Youngwer/CASA0021_GPP/APP/assets/images/Animation/R1.png

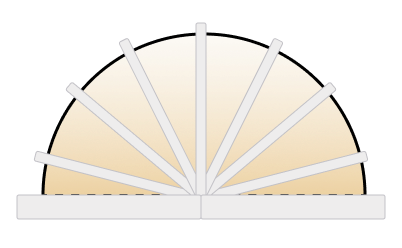
APP/assets/images/Animation/R1.png
