Youngwer/CASA0021_GPP/APP/assets/images/Animation/R3.png

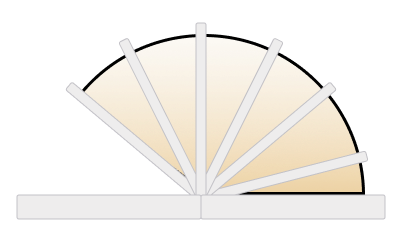
APP/assets/images/Animation/R3.png
