Youngwer/CASA0021_GPP/APP/assets/images/Animation/R6.png

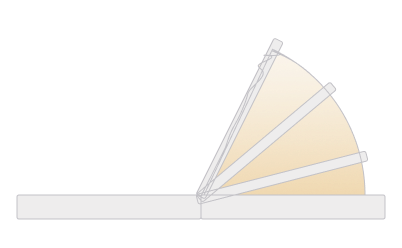
APP/assets/images/Animation/R6.png
