Youngwer/CASA0021_GPP/APP/assets/images/Animation/R7.png

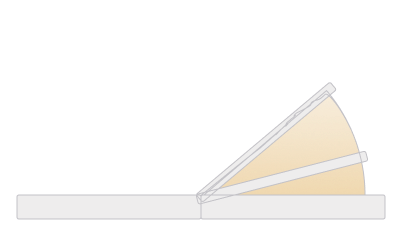
APP/assets/images/Animation/R7.png
