Youngwer/CASA0021_GPP/APP/assets/images/Animation/R8.png

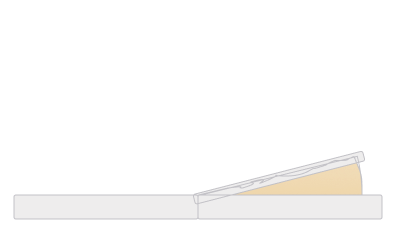
APP/assets/images/Animation/R8.png
