Youngwer/CASA0021_GPP/APP/assets/images/book2_AI.jpg

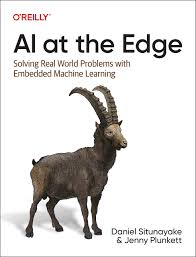
APP/assets/images/book2_AI.jpg
