Youngwer/CASA0021_GPP/APP/assets/images/book3_dominicana.jpg

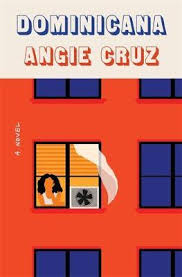
APP/assets/images/book3_dominicana.jpg
