Youngwer/CASA0021_GPP/APP/assets/images/book4_steppenwolf.jpg

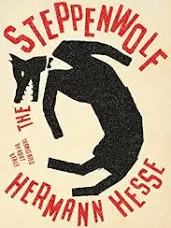
APP/assets/images/book4_steppenwolf.jpg
