Youngwer/CASA0021_GPP/APP/assets/images/book5_west.jpg

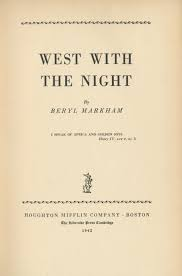
APP/assets/images/book5_west.jpg
