Youngwer/CASA0021_GPP/APP/assets/images/book6_muscle.jpg

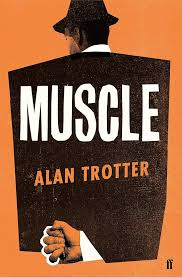
APP/assets/images/book6_muscle.jpg
