Youngwer/CASA0021_GPP/APP/assets/images/Duncan.png

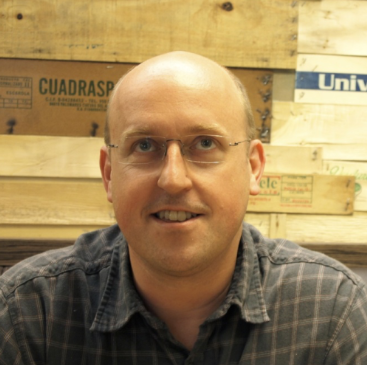
APP/assets/images/Duncan.png
