Youngwer/CASA0021_GPP/APP/assets/images/Home.png

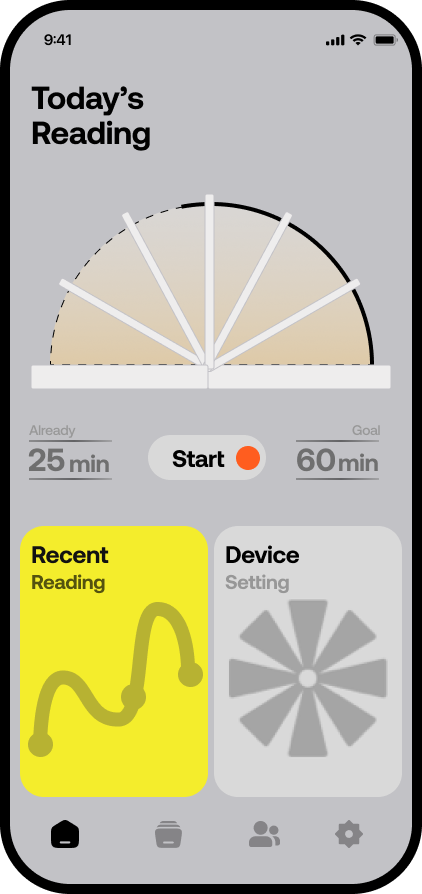
APP/assets/images/Home.png
