Youngwer/CASA0021_GPP/APP/assets/images/image2.jpg

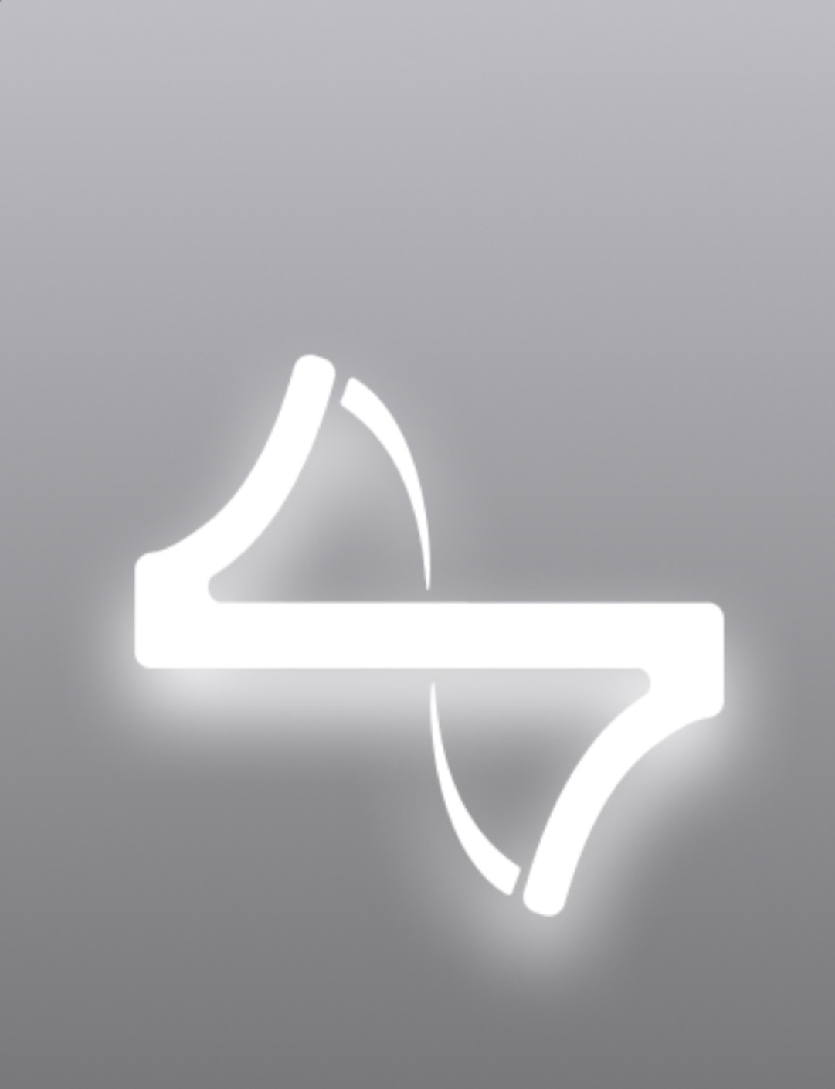
APP/assets/images/image2.jpg
