Youngwer/CASA0021_GPP/APP/assets/images/Ke.png

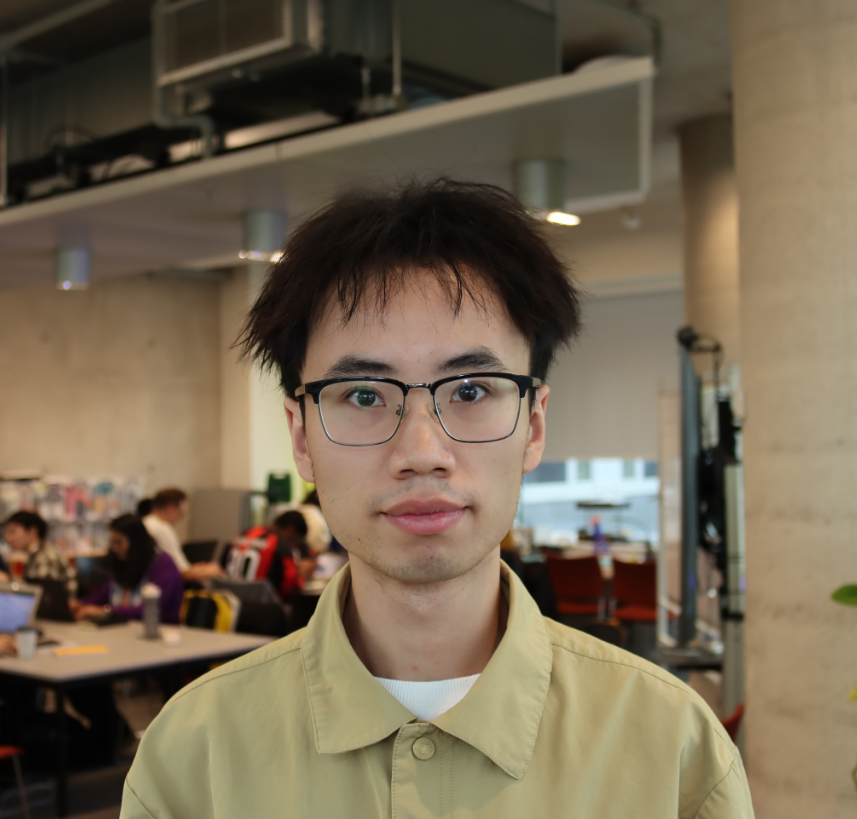
APP/assets/images/Ke.png
