Youngwer/CASA0021_GPP/APP/assets/images/Leah.png

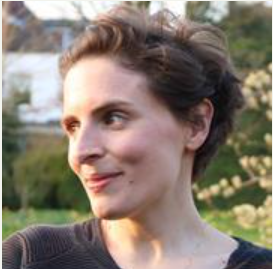
APP/assets/images/Leah.png
