Youngwer/CASA0021_GPP/APP/assets/images/Qijie.png

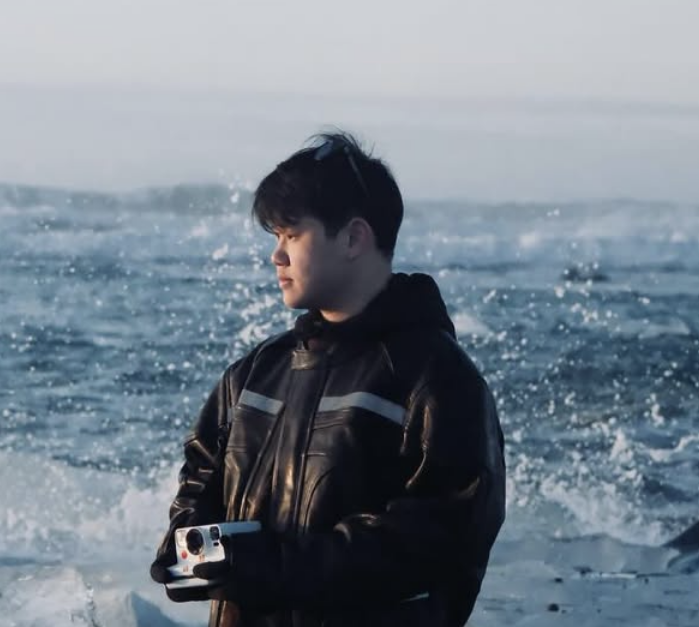
APP/assets/images/Qijie.png
