Youngwer/CASA0021_GPP/APP/assets/images/Qijing.png

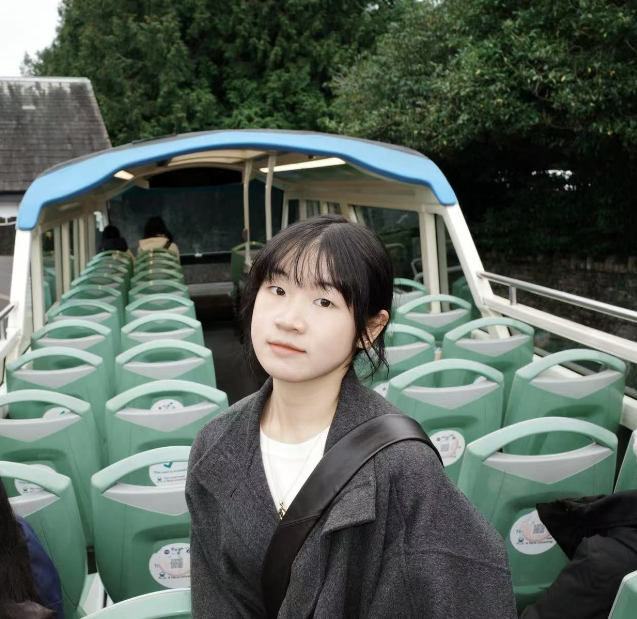
APP/assets/images/Qijing.png
