Youngwer/CASA0021_GPP/APP/assets/images/Valerio.png

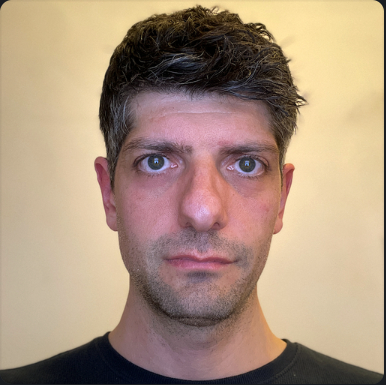
APP/assets/images/Valerio.png
