Youngwer/CASA0021_GPP/APP/assets/images/Wenhao.png

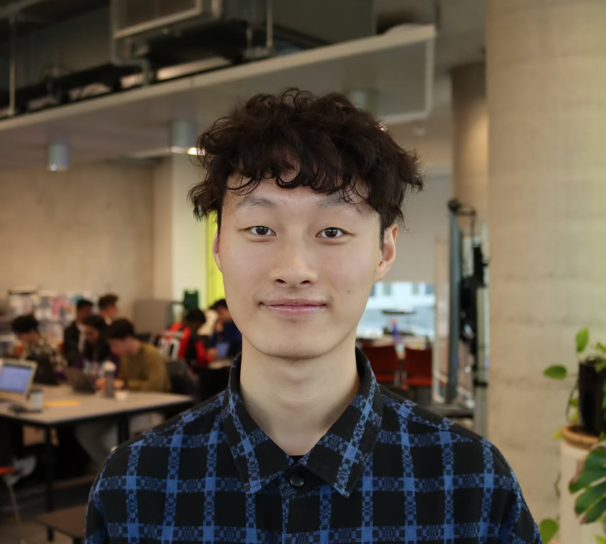
APP/assets/images/Wenhao.png
