Youngwer/CASA0021_GPP/Images/app_bookcollection.png

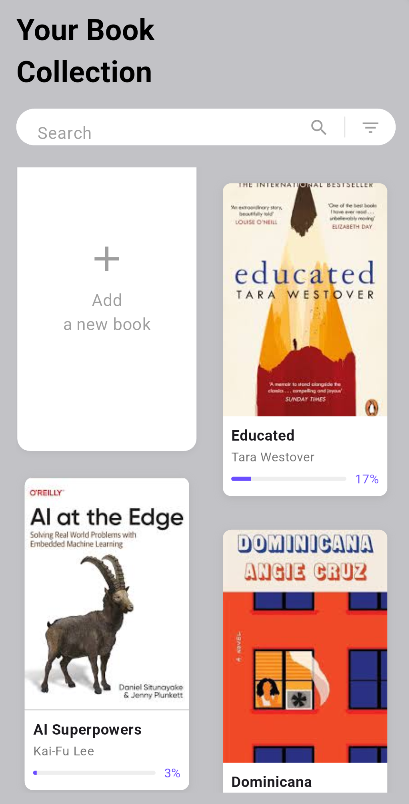
Images/app_bookcollection.png
