Youngwer/CASA0021_GPP/Images/app_data1.png

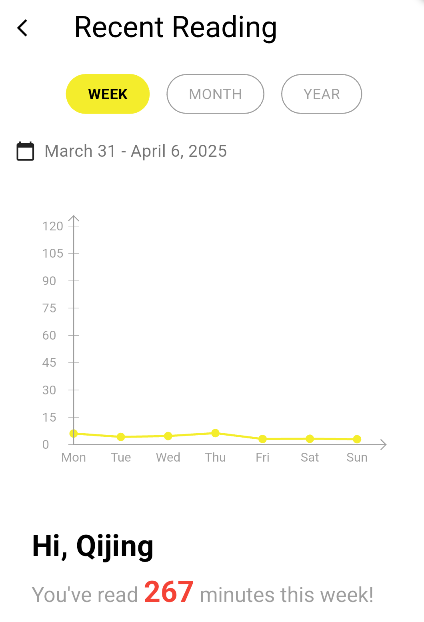
Images/app_data1.png
