Youngwer/CASA0021_GPP/Images/app_data2.png

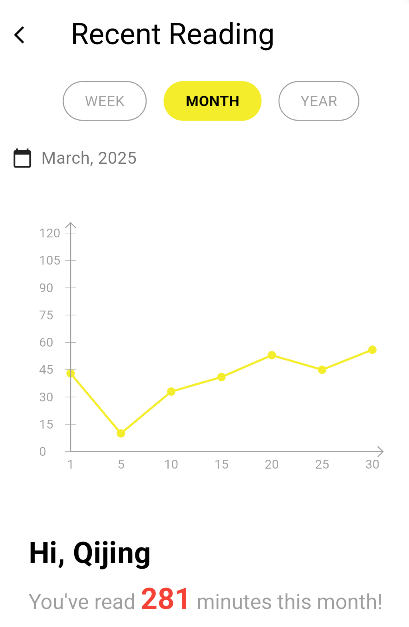
Images/app_data2.png
