Youngwer/CASA0021_GPP/Images/app_data3.png

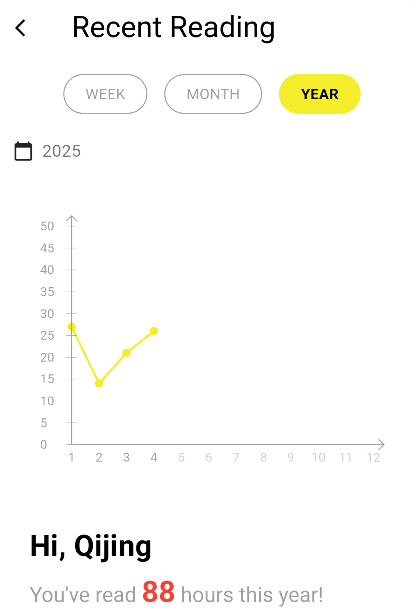
Images/app_data3.png
