Youngwer/CASA0021_GPP/Images/app_month.png

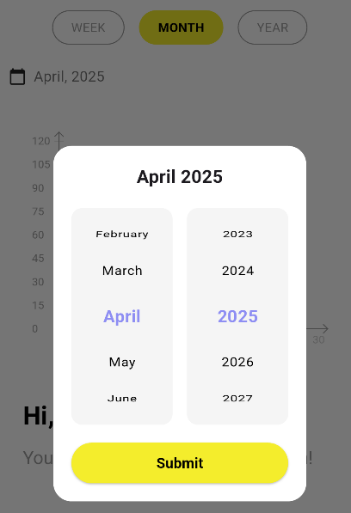
Images/app_month.png
