Youngwer/CASA0021_GPP/Images/app_recentreading.png

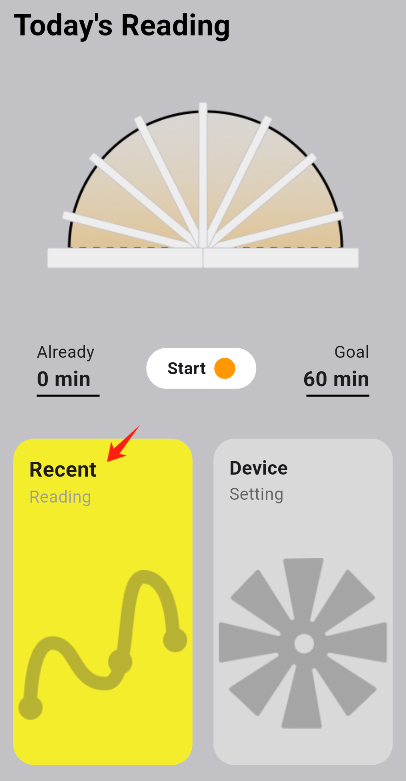
Images/app_recentreading.png
