Youngwer/CASA0021_GPP/Images/app_selectbook.png

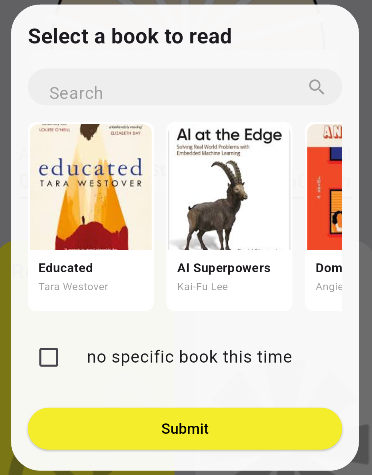
Images/app_selectbook.png
