Youngwer/CASA0021_GPP/Images/app_selectpage.png

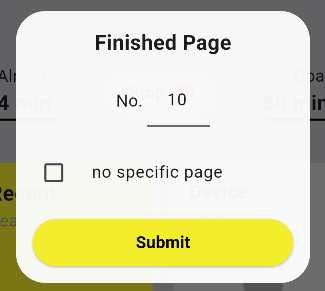
Images/app_selectpage.png
