Youngwer/CASA0021_GPP/Images/app_selecttime.png

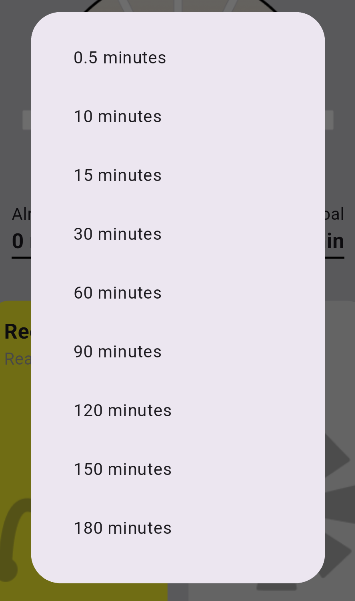
Images/app_selecttime.png
