Youngwer/CASA0021_GPP/Images/app_start.png

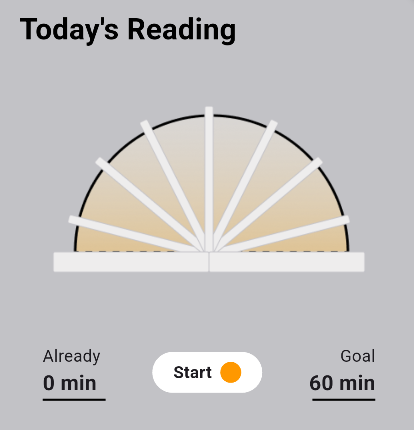
Images/app_start.png
