Youngwer/CASA0021_GPP/Images/app_year.png

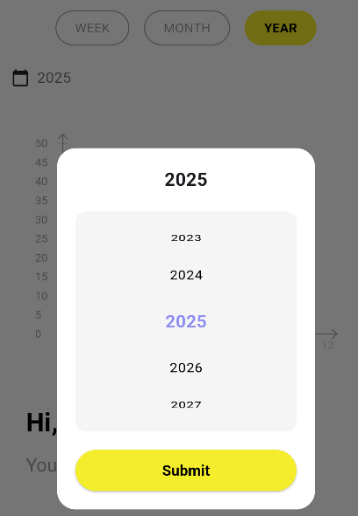
Images/app_year.png
