Youngwer/CASA0021_GPP/Images/Comparation.png

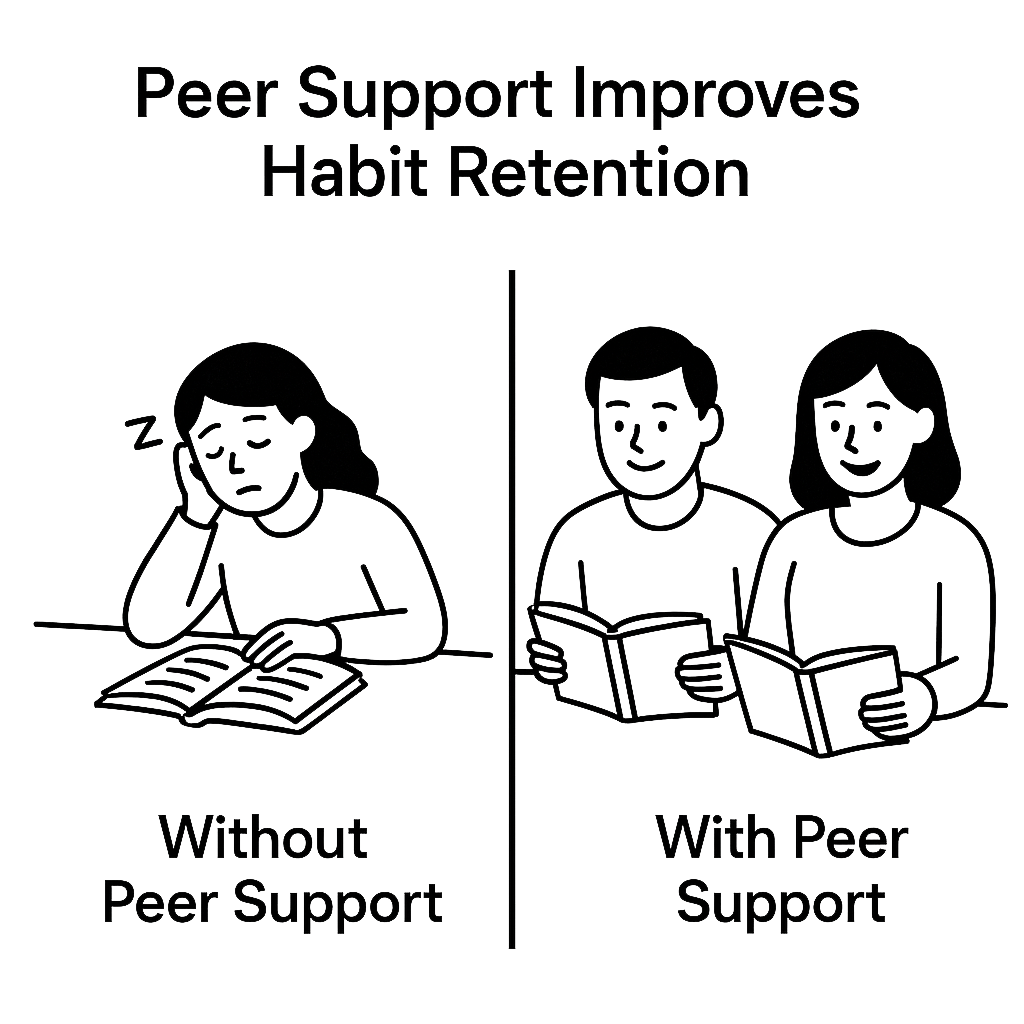
Images/Comparation.png
