Youngwer/CASA0021_GPP/Images/Data.png

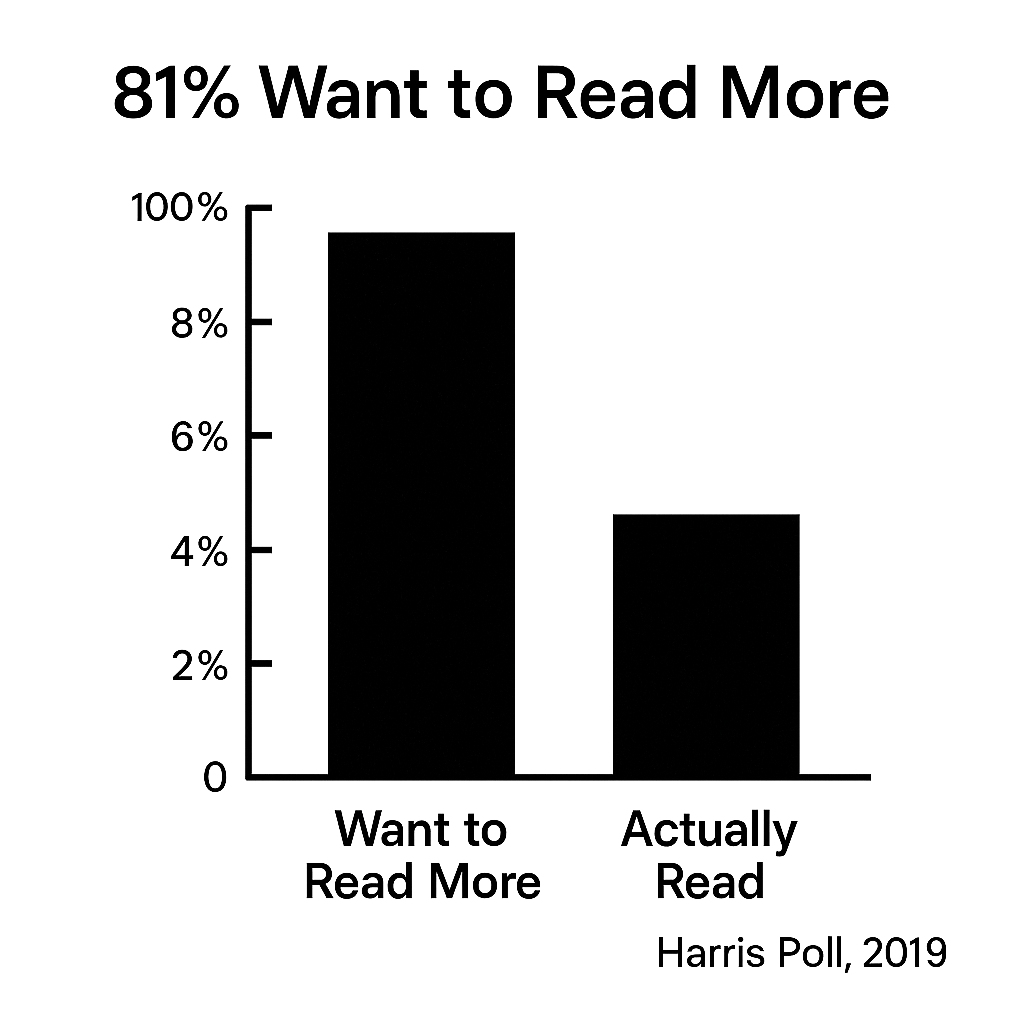
Images/Data.png
