Youngwer/CASA0021_GPP/Images/Distraction.png

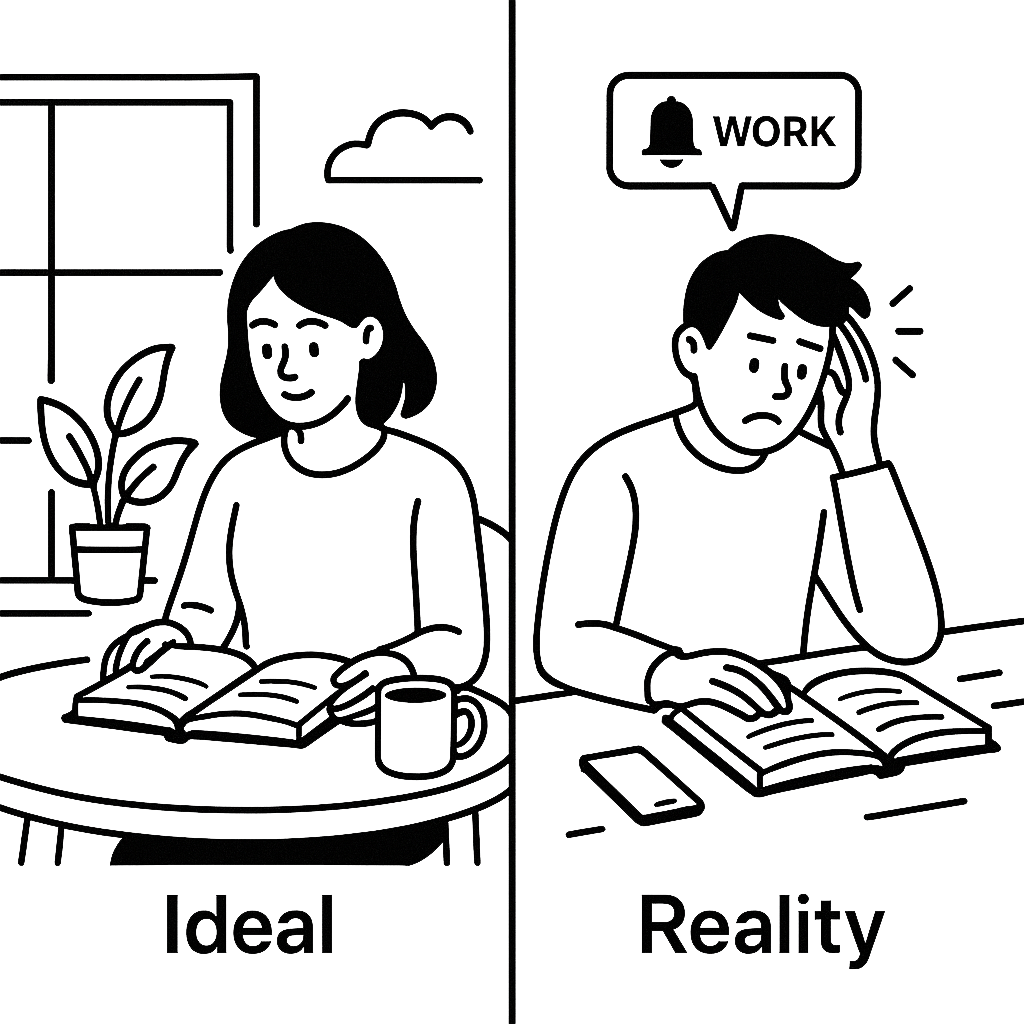
Images/Distraction.png
