Youngwer/CASA0021_GPP/Images/finalsketch.png

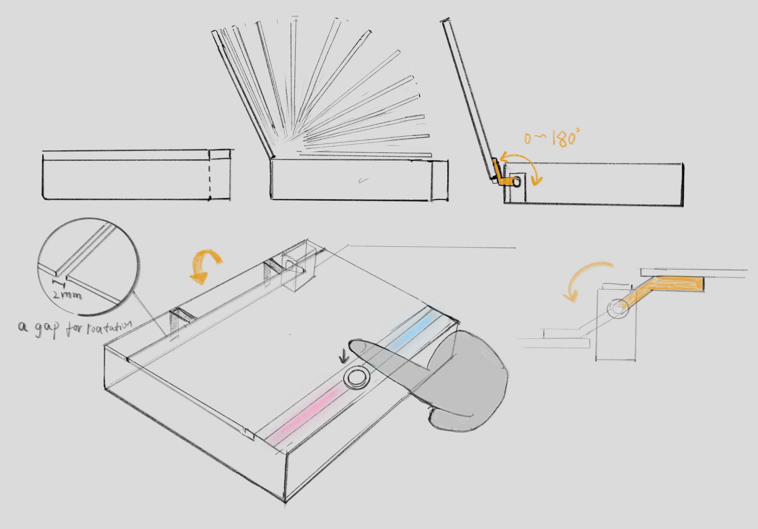
Images/finalsketch.png
