Youngwer/CASA0021_GPP/Images/flow.png

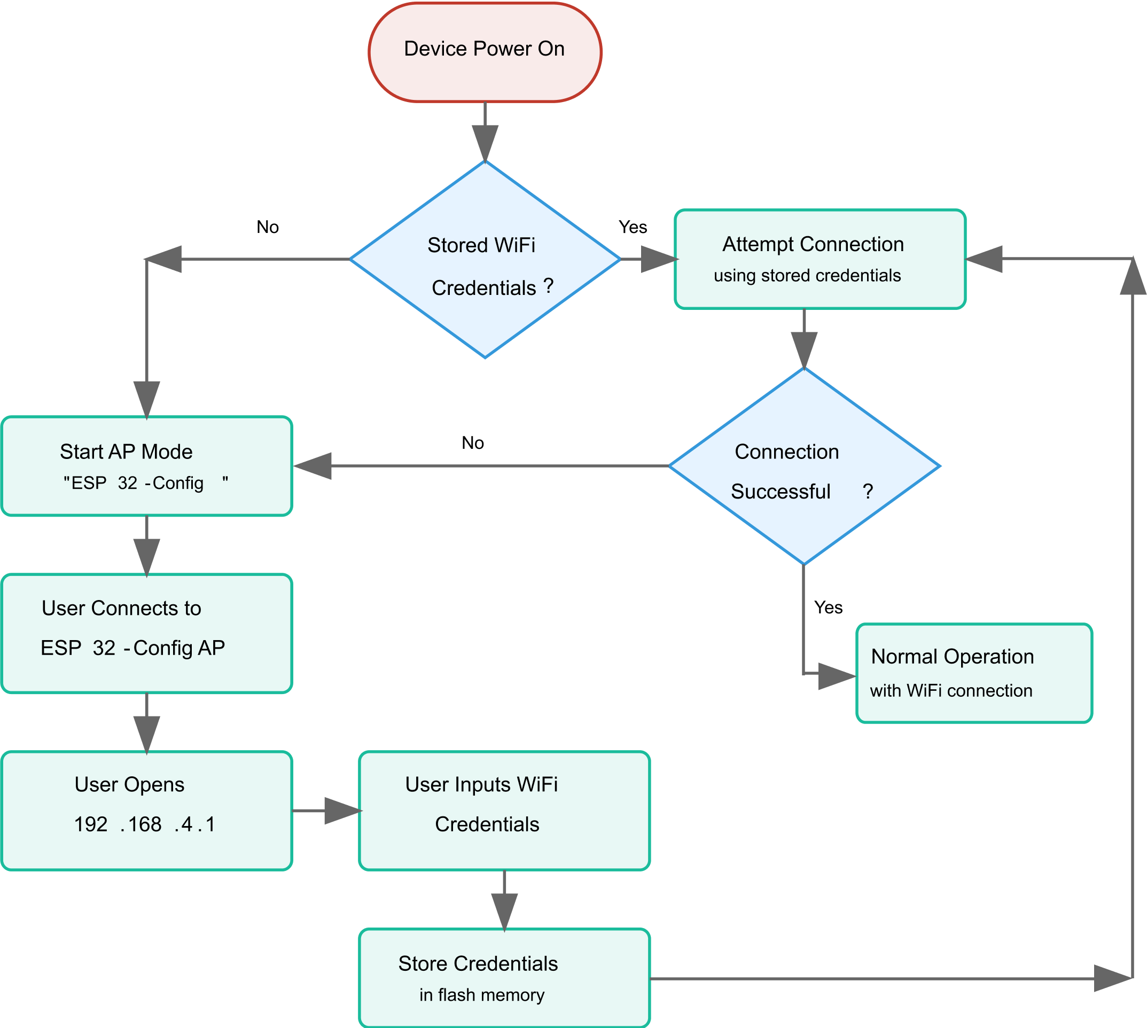
Images/flow.png
