Youngwer/CASA0021_GPP/Images/monitor.png

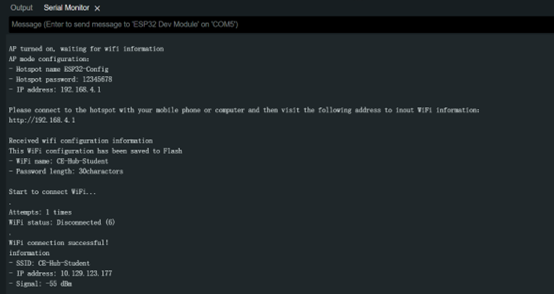
Images/monitor.png
