Youngwer/CASA0021_GPP/Images/service_blueprint_map.png

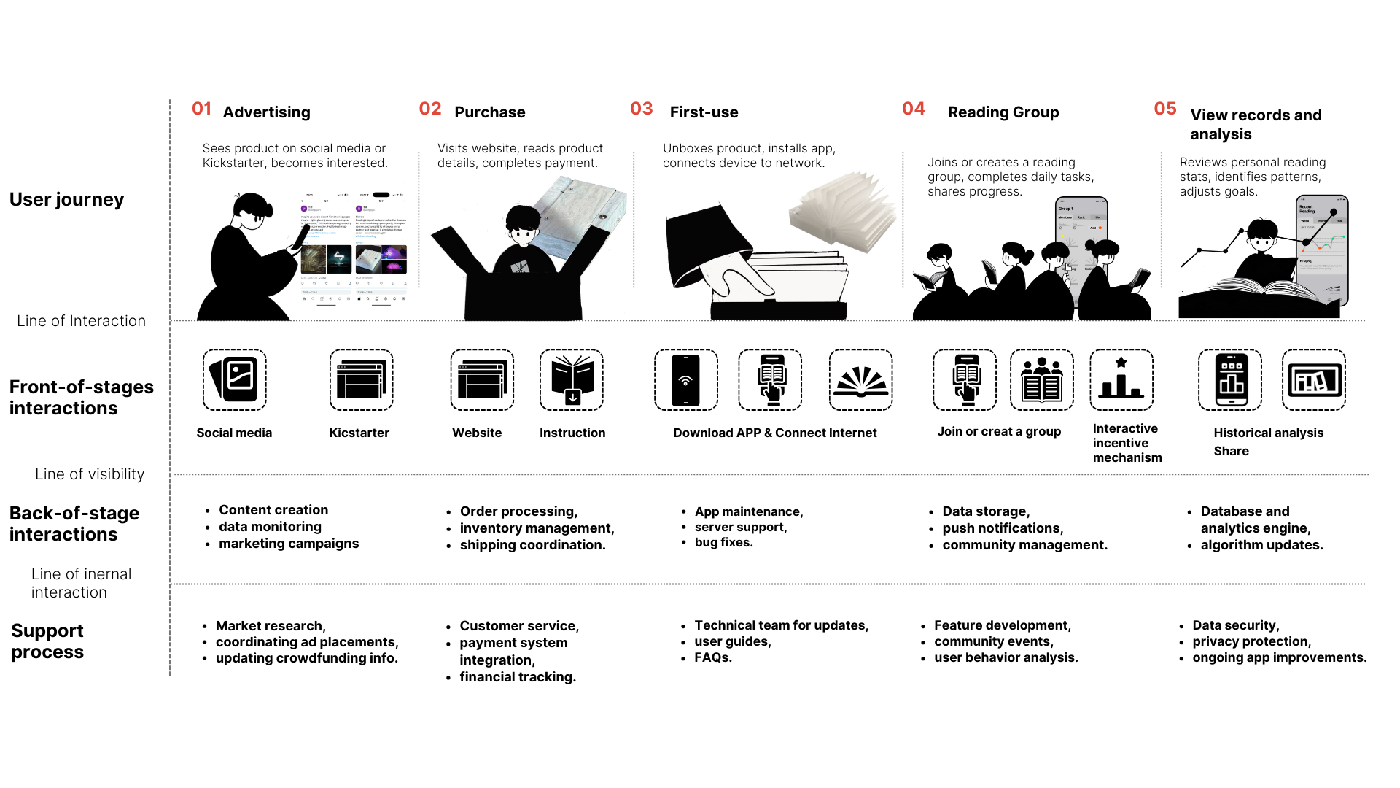
Images/service_blueprint_map.png
