Youngwer/CASA0021_GPP/Images/sketch.png

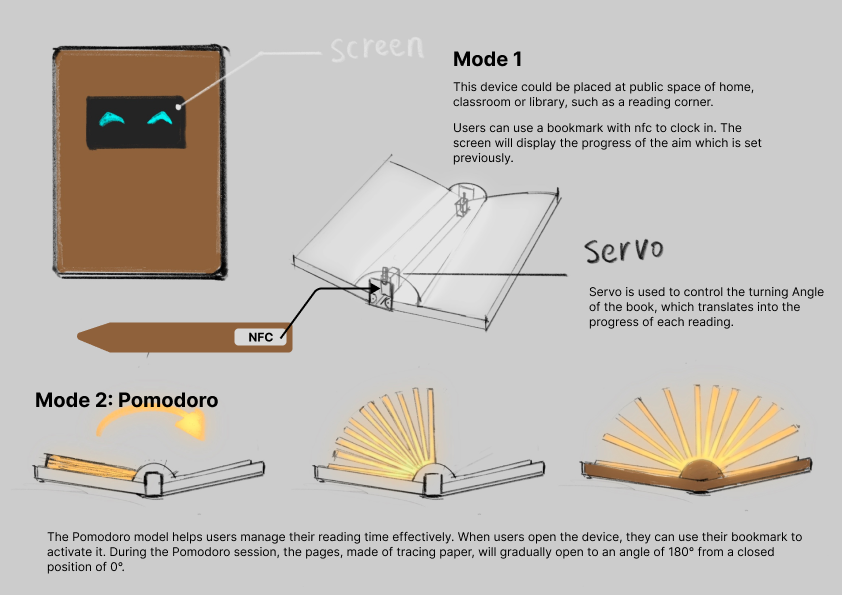
Images/sketch.png
