Youngwer/CASA0021_GPP/Images/sub.png

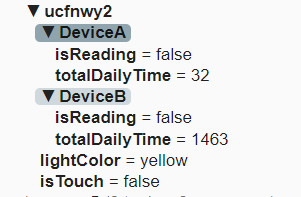
Images/sub.png
