Youngwer/CASA0021_GPP/Images/target1.png

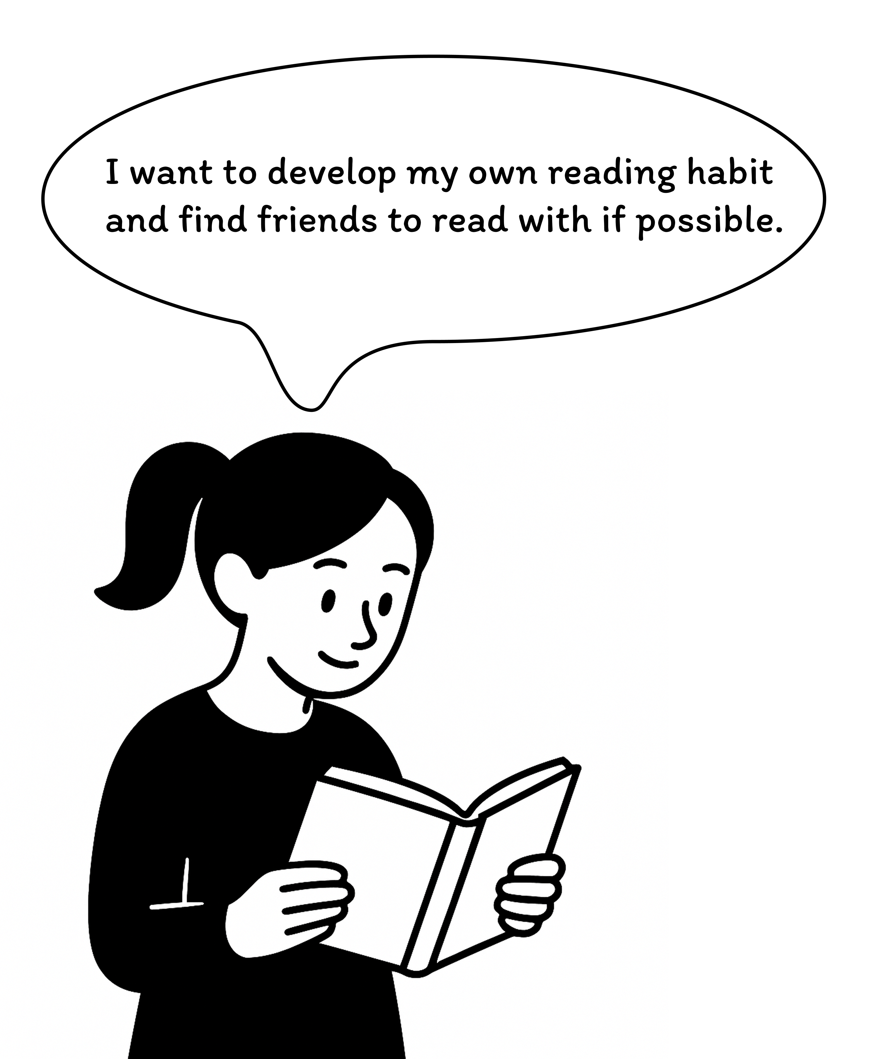
Images/target1.png
