Youngwer/CASA0021_GPP/Images/target2.png

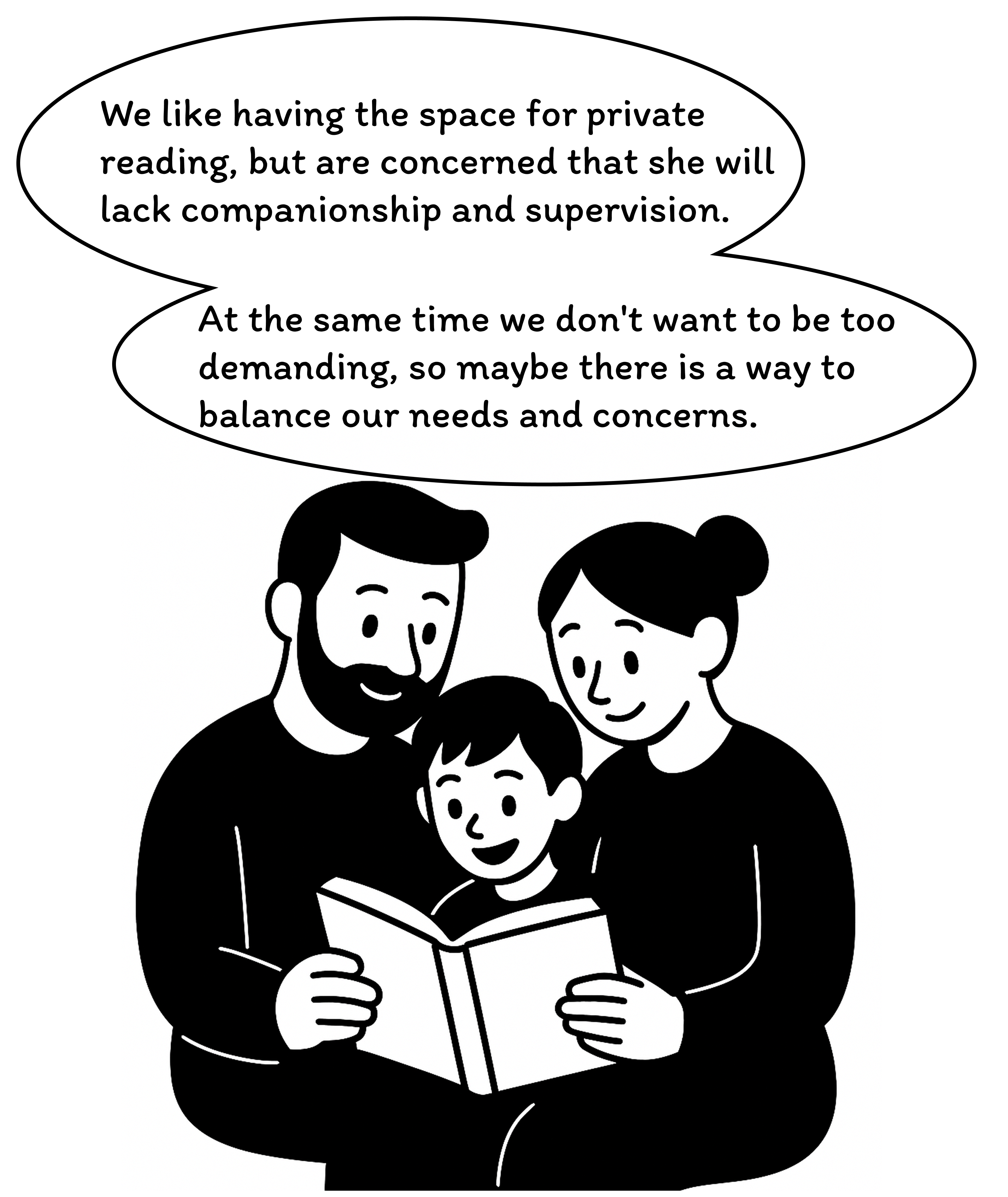
Images/target2.png
