Youngwer/CASA0021_GPP/Images/target3.png

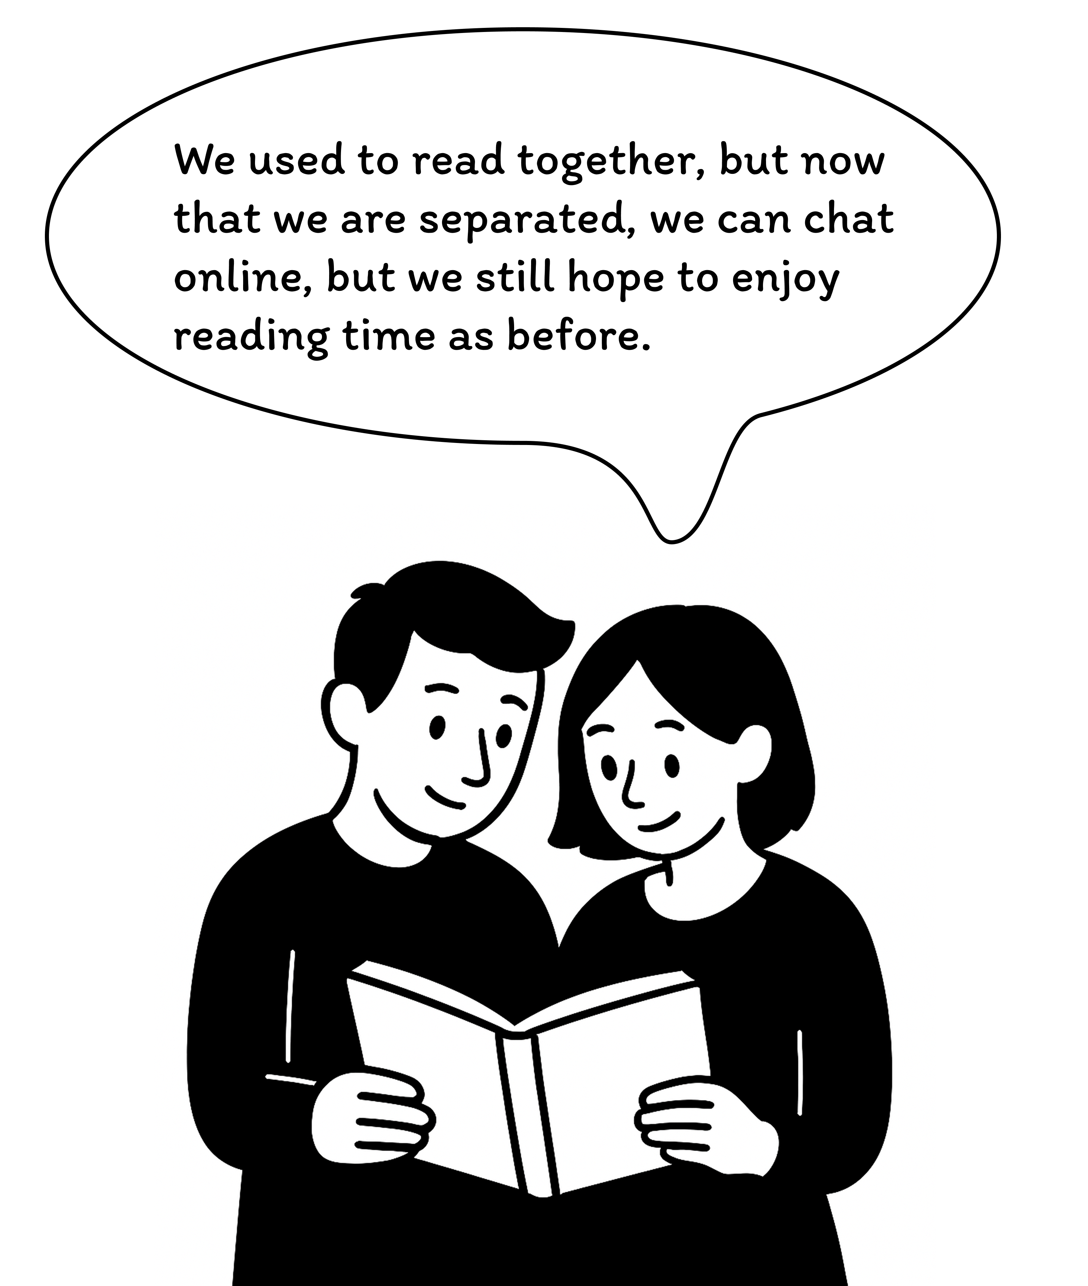
Images/target3.png
