Youngwer/CASA0021_GPP/Images/title.jpg

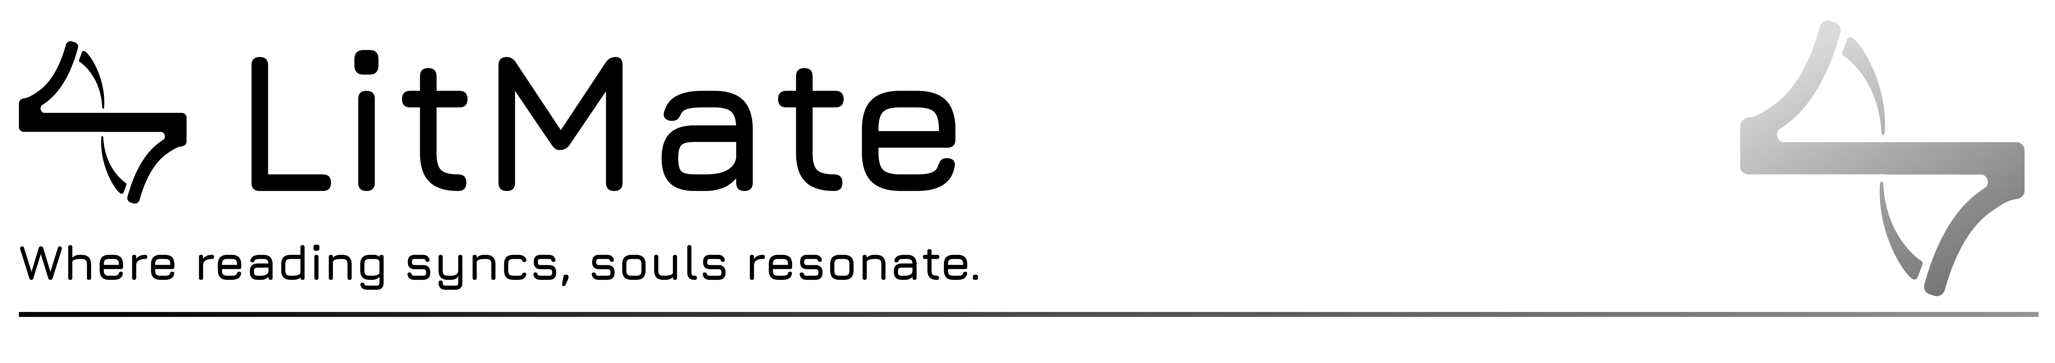
Images/title.jpg
