Youngwer/CASA0021_GPP/Images/web_interface.png

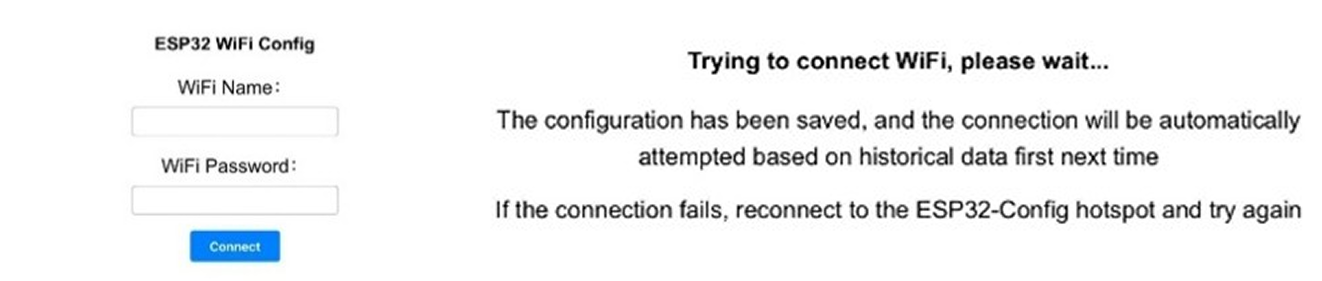
Images/web_interface.png
